jack-mumford/display-keyboard/main/main_screen.h

#pragma once

#include <string>

#include <esp_err.h>
#include <lvgl.h>

#include "event_ids.h"
#include "screen.h"

#define DISPLAY_MEMORY
#define DEBUG_STRING

constexpr lv_coord_t kAlbumArtworkWidth = 130;
constexpr lv_coord_t kAlbumArtworkHeight = 130;

class MainScreen : public Screen {
 public:
  explicit MainScreen(MainDisplay& display);
  ~MainScreen();

  esp_err_t Initialize();
  void SetWiFiStatus(WiFiStatus status);
  void UpdateTime();
#ifdef DEBUG_STRING
  void SetDebugString(const char* str);
#endif
  void SetAlbumArtwork(lv_img_dsc_t image);

 private:
  esp_err_t InitializeStatusBar();
  void UpdateWiFi();
  esp_err_t LoadWiFiImages();
  esp_err_t LoadGearImage();
  esp_err_t LoadSpotifyImage();
  esp_err_t CreateTimeLabel();
  esp_err_t CreateSongDataLabels();
  esp_err_t CreateAlbumArtwork();
  void UpdateRating();
  esp_err_t LoadRatingImages();

  lv_img_dsc_t album_cover_image_;
  lv_obj_t* lbl_test_ = nullptr;
  lv_obj_t* lbl_time_ = nullptr;
#ifdef DEBUG_STRING
  lv_obj_t* lbl_debug_msg_ = nullptr;
#endif
#ifdef DISPLAY_MEMORY
  lv_obj_t* lbl_memory_spiram_ = nullptr;
  lv_obj_t* lbl_memory_internal_ = nullptr;
#endif
  lv_obj_t* img_album_ = nullptr;
  lv_obj_t* img_wifi_online_ = nullptr;
  lv_obj_t* img_wifi_offline_ = nullptr;
  lv_obj_t* img_spotify_ = nullptr;
  lv_obj_t* img_gear_ = nullptr;
  lv_obj_t* img_thumbs_none_ = nullptr;
  lv_obj_t* img_thumbs_up_ = nullptr;
  std::string last_time_;
  WiFiStatus wifi_status_ = WiFiStatus::Offline;
};
