jack-mumford/display-keyboard/main/wifi.cc

#include "wifi.h"

#include <cstring>

#define LOG_LOCAL_LEVEL ESP_LOG_VERBOSE
#include <esp_log.h>
#include <esp_wifi.h>

#include "event_ids.h"

namespace {
constexpr char TAG[] = "WiFi";
constexpr size_t kMaxSSIDLen = 31;
constexpr size_t kMaxKeyLen = 63;
constexpr int kMaxNumConnectRetry = 10;

const char* wifi_event_name(wifi_event_t event) {
  switch (event) {
    case WIFI_EVENT_WIFI_READY:
      return "WIFI_EVENT_WIFI_READY";
    case WIFI_EVENT_SCAN_DONE:
      return "WIFI_EVENT_SCAN_DONE";
    case WIFI_EVENT_STA_START:
      return "WIFI_EVENT_STA_START";
    case WIFI_EVENT_STA_STOP:
      return "WIFI_EVENT_STA_STOP";
    case WIFI_EVENT_STA_CONNECTED:
      return "WIFI_EVENT_STA_CONNECTED";
    case WIFI_EVENT_STA_DISCONNECTED:
      return "WIFI_EVENT_STA_DISCONNECTED";
    case WIFI_EVENT_STA_AUTHMODE_CHANGE:
      return "WIFI_EVENT_STA_AUTHMODE_CHANGE";
    case WIFI_EVENT_STA_WPS_ER_SUCCESS:
      return "WIFI_EVENT_STA_WPS_ER_SUCCESS";
    case WIFI_EVENT_STA_WPS_ER_FAILED:
      return "WIFI_EVENT_STA_WPS_ER_FAILED";
    case WIFI_EVENT_STA_WPS_ER_TIMEOUT:
      return "WIFI_EVENT_STA_WPS_ER_TIMEOUT";
    case WIFI_EVENT_STA_WPS_ER_PIN:
      return "WIFI_EVENT_STA_WPS_ER_PIN";
    case WIFI_EVENT_STA_WPS_ER_PBC_OVERLAP:
      return "WIFI_EVENT_STA_WPS_ER_PBC_OVERLAP";
    case WIFI_EVENT_AP_START:
      return "WIFI_EVENT_AP_START";
    case WIFI_EVENT_AP_STOP:
      return "WIFI_EVENT_AP_STOP";
    case WIFI_EVENT_AP_STACONNECTED:
      return "WIFI_EVENT_AP_STACONNECTED";
    case WIFI_EVENT_AP_STADISCONNECTED:
      return "WIFI_EVENT_AP_STADISCONNECTED";
    case WIFI_EVENT_AP_PROBEREQRECVED:
      return "WIFI_EVENT_AP_PROBEREQRECVED";
    case WIFI_EVENT_FTM_REPORT:
      return "WIFI_EVENT_FTM_REPORT";
    case WIFI_EVENT_MAX:
      return "WIFI_EVENT_MAX";
    default:
      return "<unknown: wifi_event_t>";
  }
}

const char* ip_event_name(ip_event_t event) {
  switch (event) {
    case IP_EVENT_STA_GOT_IP:
      return "IP_EVENT_STA_GOT_IP";
    case IP_EVENT_STA_LOST_IP:
      return "IP_EVENT_STA_LOST_IP";
    case IP_EVENT_AP_STAIPASSIGNED:
      return "IP_EVENT_AP_STAIPASSIGNED";
    case IP_EVENT_GOT_IP6:
      return "IP_EVENT_GOT_IP6";
    case IP_EVENT_ETH_GOT_IP:
      return "IP_EVENT_ETH_GOT_IP";
    case IP_EVENT_PPP_GOT_IP:
      return "IP_EVENT_PPP_GOT_IP";
    case IP_EVENT_PPP_LOST_IP:
      return "IP_EVENT_PPP_LOST_IP";
    default:
      return "<unknown: ip_event_t>";
  }
}

void SafeStrCopy(char* dst, const char* src, size_t len) {
  std::strncpy(dst, src, len);
  dst[len - 1] = '\0';
}

esp_err_t GetHostname(esp_netif_t* netif, std::string* hostname) {
  const char* name(nullptr);
  const esp_err_t err = esp_netif_get_hostname(netif, &name);
  if (err != ESP_OK) {
    ESP_LOGD(TAG, "Can't get hostname: %s", esp_err_to_name(err));
    return err;
  }
  *hostname = name ? name : "";
  return ESP_OK;
}

esp_err_t GetIPAddress(esp_netif_t* netif, esp_ip4_addr_t* addr) {
  esp_netif_ip_info_t info;
  const esp_err_t err = esp_netif_get_ip_info(netif, &info);
  if (err != ESP_OK) {
    ESP_LOGD(TAG, "Can't get assigned IP address: %s", esp_err_to_name(err));
    return err;
  }
  *addr = info.ip;
  return ESP_OK;
}

}  // namespace

void WiFi::HandleWiFiEvent(wifi_event_t event_id, void* event_data) {
  ESP_LOGV(TAG, "Wi-Fi event: %s", wifi_event_name(event_id));
  switch (event_id) {
    case WIFI_EVENT_STA_START:
      ESP_LOGW(TAG, "Starting");
      esp_wifi_connect();
      break;
    case WIFI_EVENT_STA_DISCONNECTED:
      if (retry_num_ < kMaxNumConnectRetry) {
        esp_wifi_connect();
        retry_num_++;
      } else {
        ESP_LOGW(TAG, "Connection failed");
        xEventGroupSetBits(wifi_event_group_, EVENT_NETWORK_DISCONNECTED);
      }
      break;
    default:
      break;
  }
}

void WiFi::HandleIPEvent(ip_event_t event_id, void* event_data) {
  ESP_LOGV(TAG, "IP event: %s", ip_event_name(event_id));
  switch (event_id) {
    case IP_EVENT_STA_GOT_IP: {
      const ip_event_got_ip_t* event =
          static_cast<ip_event_got_ip_t*>(event_data);
      ESP_LOGI(TAG, "Got ip:" IPSTR, IP2STR(&event->ip_info.ip));
      std::string hostname = "?";
      ::GetHostname(event->esp_netif, &hostname);
      ESP_LOGI(TAG, "Hostname: \"%s\"", hostname.c_str());

      retry_num_ = 0;
      xEventGroupSetBits(wifi_event_group_, EVENT_NETWORK_GOT_IP);
    } break;
    default:
      break;
  }
}

// static
void WiFi::EventHandler(void* arg,
                        esp_event_base_t event_base,
                        int32_t event_id,
                        void* event_data) {
  if (event_base == WIFI_EVENT) {
    static_cast<WiFi*>(arg)->HandleWiFiEvent(
        static_cast<wifi_event_t>(event_id), event_data);
  } else if (event_base == IP_EVENT) {
    static_cast<WiFi*>(arg)->HandleIPEvent(static_cast<ip_event_t>(event_id),
                                           event_data);
  }
}

WiFi::WiFi(EventGroupHandle_t wifi_event_group)
    : wifi_event_group_(wifi_event_group),
      instance_any_id_(nullptr),
      instance_got_ip_(nullptr),
      retry_num_(0),
      netif_(nullptr) {}

WiFi::~WiFi() {
  if (instance_got_ip_) {
    ESP_ERROR_CHECK(esp_event_handler_instance_unregister(
        IP_EVENT, IP_EVENT_STA_GOT_IP, instance_got_ip_));
  }
  if (instance_any_id_) {
    ESP_ERROR_CHECK(esp_event_handler_instance_unregister(
        WIFI_EVENT, ESP_EVENT_ANY_ID, instance_any_id_));
  }
}

esp_err_t WiFi::Inititialize() {
  esp_err_t err = esp_netif_init();
  if (err != ESP_OK) {
    ESP_LOGE(TAG, "netif init failed: %s", esp_err_to_name(err));
    return err;
  }

  esp_netif_t* netif_ = esp_netif_create_default_wifi_sta();
  if (!netif_)
    return ESP_FAIL;

  const wifi_init_config_t cfg = WIFI_INIT_CONFIG_DEFAULT();
  err = esp_wifi_init(&cfg);
  if (err != ESP_OK) {
    ESP_LOGE(TAG, "esp_wifi_init failed: %s", esp_err_to_name(err));
    return err;
  }

  err = esp_event_handler_instance_register(
      WIFI_EVENT, ESP_EVENT_ANY_ID, &EventHandler, this, &instance_any_id_);
  if (err != ESP_OK) {
    ESP_LOGE(TAG, "esp_event_handler_instance_register failed: %s",
             esp_err_to_name(err));
    return err;
  }
  err = esp_event_handler_instance_register(
      IP_EVENT, IP_EVENT_STA_GOT_IP, &EventHandler, this, &instance_got_ip_);

  return err;
}

esp_err_t WiFi::InitiateConnection(const std::string& ssid,
                                   const std::string& key) {
  ESP_LOGI(TAG, "Attempting connection to WiFi network: \"%s\"", ssid.c_str());

  esp_wifi_stop();
  // TODO: Is clearing events necessary, or is this done automatically?
  constexpr EventBits_t kAllNetworkEvents =
      EVENT_NETWORK_GOT_IP | EVENT_NETWORK_DISCONNECTED;
  xEventGroupClearBits(wifi_event_group_, kAllNetworkEvents);

  retry_num_ = 0;

  if (ssid.length() > kMaxSSIDLen || key.length() > kMaxKeyLen)
    return ESP_ERR_INVALID_SIZE;

  esp_err_t err = esp_wifi_set_mode(WIFI_MODE_STA);
  if (err != ESP_OK) {
    ESP_LOGE(TAG, "Failure to set mode: %s", esp_err_to_name(err));
    return err;
  }

  wifi_config_t wifi_config = {
      .sta =
          {
              .ssid = {0},
              .password = {0},
              .scan_method = WIFI_FAST_SCAN,
              .bssid_set = false,
              .bssid = {0},
              .channel = 0,
              .listen_interval = 0,
              .sort_method = WIFI_CONNECT_AP_BY_SIGNAL,
              .threshold{
                  .rssi = 0,
                  .authmode = WIFI_AUTH_WPA2_PSK,
              },
              .pmf_cfg = {.capable = true, .required = false},
#if ESP_IDF_VERSION >= ESP_IDF_VERSION_VAL(4, 3, 0)
              .rm_enabled = false,
              .btm_enabled = false,
              .reserved = 0,
#endif
          },
  };
  SafeStrCopy(reinterpret_cast<char*>(wifi_config.sta.ssid), ssid.c_str(),
              sizeof(wifi_config.sta.ssid) - 1);
  SafeStrCopy(reinterpret_cast<char*>(wifi_config.sta.password), key.c_str(),
              sizeof(wifi_config.sta.password) - 1);

  err = esp_wifi_set_config(WIFI_IF_STA, &wifi_config);
  if (err != ESP_OK) {
    ESP_LOGE(TAG, "Failure to set config: %s", esp_err_to_name(err));
    return err;
  }

  err = esp_wifi_start();
  if (err != ESP_OK)
    ESP_LOGE(TAG, "Start failed: %s", esp_err_to_name(err));

  return err;
}

esp_err_t WiFi::GetHostname(std::string* hostname) const {
  return ::GetHostname(netif_, hostname);
}

esp_err_t WiFi::GetIPAddress(esp_ip4_addr_t* addr) const {
  return ::GetIPAddress(netif_, addr);
}
