jack-mumford/display-keyboard/main/keyboard.h

#pragma once

#include <array>

#include <esp_err.h>
#include <i2clib/master.h>
#include <i2clib/operation.h>

namespace kbd {
namespace adp5589 {
enum class RegNum : uint8_t;

namespace reg {
struct FIFO;
struct ID;
struct INT_STATUS;
struct PIN_CONFIG_A;
struct PIN_CONFIG_B;
struct PIN_CONFIG_C;
struct Status;
}  // namespace reg
}  // namespace adp5589
}  // namespace kbd

// Maximum number of HID_KEY_* key codes.
constexpr size_t kNumHIDKeyCodes = 0xff;

class Keyboard {
 public:
  explicit Keyboard(i2c::Master i2c_master);
  ~Keyboard();

  /**
   * Reset the keyboard IC to manufacturer default values.
   */
  esp_err_t Reset();

  /**
   * Initialize the keyboard.
   *
   * Call after reset to configure the keyboard IC.
   */
  esp_err_t Initialize();

  /**
   * Handle any keyboard events.
   *
   * Call this function, either polled or when interrupt pin indicates, to
   * handle any queued keyboard events.
   */
  esp_err_t HandleEvents();

 private:
  /**
   * Report all HID events to the USB host.
   */
  esp_err_t ReportHIDEvents();
  esp_err_t WriteByte(kbd::adp5589::RegNum reg, uint8_t value);
  esp_err_t ReadByte(kbd::adp5589::RegNum reg, uint8_t* value);
  esp_err_t Read(kbd::adp5589::reg::FIFO* reg);
  esp_err_t Read(kbd::adp5589::reg::ID* reg);
  esp_err_t Read(kbd::adp5589::reg::INT_STATUS* reg);
  esp_err_t Read(kbd::adp5589::reg::Status* reg);
  esp_err_t InitializeKeys(i2c::Operation& op);
  esp_err_t InitializeInterrupts(i2c::Operation& op);

  i2c::Master i2c_master_;

  /**
   * Array used to map TinyUSB's HID KEYCODE value to the button
   * pressed/depressed state.
   */
  std::array<bool, kNumHIDKeyCodes> key_states_;  // true if depressed.
  uint32_t event_number_ = 0;
};
