jack-mumford/display-keyboard/make.py

#!/usr/bin/env python3

import errno
import glob
import os
import platform
import serial.tools.list_ports
import subprocess
import sys
from pprint import pprint


class SdkConfigManager(object):
    @staticmethod
    def GetConsoleTarget(sdkconfig):
        if 'CONFIG_ESP_CONSOLE_UART' in sdkconfig and \
                sdkconfig['CONFIG_ESP_CONSOLE_UART'] == 'y':
            return 'UART'
        if 'CONFIG_ESP_CONSOLE_CDC' in sdkconfig and \
                sdkconfig['CONFIG_ESP_CONSOLE_CDC'] == 'y':
            return 'CDC'
        if 'CONFIG_ESP_CONSOLE_CUSTOM' in sdkconfig and \
                sdkconfig['CONFIG_ESP_CONSOLE_CUSTOM'] == 'y':
            return 'CUSTOM'
        return 'NONE'

    @staticmethod
    def Load():
        values = dict()
        try:
            with open('sdkconfig', 'r') as f:
                for line in f.readlines():
                    line = line.strip()
                    if len(line) < 1:
                        continue
                    if line[0] == '#':
                        continue
                    items = line.split('=')
                    if len(items) != 2:
                        print(line)
                    if items[0] in values:
                        print('Already have: ' + line)
                    values[items[0]] = items[1]
        except FileNotFoundError:
            pass
        return values


class PortManager(object):
    ignored = ('/dev/cu.Bluetooth-Incoming-Port')

    def __init__(self, sdkconfig):
        self.__sdkconfig = sdkconfig
        self.__console_target = SdkConfigManager.GetConsoleTarget(sdkconfig)

    @staticmethod
    def __GetSerialWildcard():
        return '/dev/cu.usbserial-*'

    @staticmethod
    def __GetModemWildcard():
        return '/dev/cu.usbmodem*'

    @staticmethod
    def __GetMatchingPorts(wildcard):
        ports = []
        for file in glob.glob(wildcard, recursive=False):
            if file in PortManager.ignored:
                continue
            ports.append(file)
        return ports

    @staticmethod
    def __GetDevicePorts():
        """Return any port with "USB Serial Device in the description.

        The ESP32 port is one of these.
        """
        ports = []
        for port in serial.tools.list_ports.comports():
            if (port.hwid and 'SER=0' in port.hwid):
                ports.append(port.device)
            # pprint(vars(port))
        return ports

    @staticmethod
    def __GetCOMPorts():
        """Return any port with "USB Serial Port" in the description.

        The serial debugger shows up as one of these.
        """
        ports = []
        for port in serial.tools.list_ports.comports():
            if (port.hwid and 'SER=0' not in port.hwid):
                ports.append(port.device)
            # pprint(vars(port))
        return ports

    @staticmethod
    def GetSerialPorts():
        if platform.system() == 'Windows':
            return PortManager.__GetCOMPorts()
        return PortManager.__GetMatchingPorts(
            PortManager.__GetSerialWildcard())

    @staticmethod
    def GetModemPorts():
        if platform.system() == 'Windows':
            return PortManager.__GetDevicePorts()
        return PortManager.__GetMatchingPorts(PortManager.__GetModemWildcard())

    @staticmethod
    def GetFlashPort():
        ports = PortManager.GetModemPorts()
        if ports:
            return ports[0]
        ports = PortManager.GetSerialPorts()
        return ports[0] if ports else None

    def GetMonitorPort(self):
        if self.__console_target == 'UART':
            ports = PortManager.GetSerialPorts()
        else:
            ports = PortManager.GetModemPorts()
        return ports[0] if ports else None

    def PrintPorts(self, fd=sys.stdout):
        print('Serial ports: %s' % PortManager.GetSerialPorts(), file=fd)
        print('Modem ports: %s' % PortManager.GetSerialPorts(), file=fd)
        print('Flash port: %s' % PortManager.GetFlashPort(), file=fd)
        print('Monitor port: %s' % self.GetMonitorPort(), file=fd)


def TargetNeedsMonitorPort(target):
    return target in ('monitor')


def TargetNeedsFlashPort(target):
    return target in ('flash', 'app-flash', 'flash-erase', 'manual-flash',
                      'flash-feathers2-stock-bootloader')


def MakeTargets(targets, port_manager):
    flash_port = PortManager.GetFlashPort()
    monitor_port = port_manager.GetMonitorPort()
    for target in targets:
        if TargetNeedsMonitorPort(target) and not monitor_port:
            print("Target \"%s\" needs a monitor port, but can't find one." %
                  target,
                  file=sys.stderr)
            port_manager.PrintPorts(sys.stderr)
            sys.exit(errno.ENODEV)
        if TargetNeedsFlashPort(target) and not flash_port:
            print("Target \"%s\" needs a flash port, but can't find one." %
                  target,
                  file=sys.stderr)
            port_manager.PrintPorts(sys.stderr)
            sys.exit(errno.ENODEV)
    if flash_port:
        os.environ["FLASH_PORT"] = flash_port
    if monitor_port:
        os.environ["MONITOR_PORT"] = monitor_port
    cmd = ['make', '--file=Makefile-build']
    cmd.extend(targets)
    subprocess.check_call(cmd)


if 'IDF_PATH' not in os.environ:
    print('ESP-IDF environment not sourced. Run:', file=sys.stderr)
    print(file=sys.stderr)
    print('. $HOME/esp/esp-idf/export.sh', file=sys.stderr)
    print(file=sys.stderr)
    sys.exit(1)

port_manager = PortManager(SdkConfigManager.Load())

targets = sys.argv[1:]
MakeTargets(targets, port_manager)
