jack-mumford/display-keyboard/main/event_ids.h

#pragma once

#include <freertos/include/freertos/FreeRTOS.h>

#include <freertos/include/freertos/event_groups.h>

constexpr EventBits_t EVENT_NETWORK_GOT_IP = BIT0;
constexpr EventBits_t EVENT_NETWORK_DISCONNECTED = BIT1;
constexpr EventBits_t EVENT_SPOTIFY_GOT_AUTHORIZATION_CODE = BIT2;
constexpr EventBits_t EVENT_SPOTIFY_ACCESS_TOKEN_GOOD = BIT3;
constexpr EventBits_t EVENT_SPOTIFY_ACCESS_TOKEN_FAILURE = BIT4;
constexpr EventBits_t EVENT_SPOTIFY_ACCESS_TOKEN_EXPIRE = BIT5;
constexpr EventBits_t EVENT_ALL = BIT0 | BIT1 | BIT2 | BIT3 | BIT4 | BIT5;

enum class WiFiStatus {
  Offline,
  Online,
};
