jack-mumford/display-keyboard/main/resource_fetcher.h

#pragma once

#include <cstdint>
#include <memory>
#include <queue>
#include <string>
#include <vector>

#include <freertos/include/freertos/FreeRTOS.h>
#include <freertos/include/freertos/event_groups.h>
#include <freertos/include/freertos/semphr.h>
#include <freertos/include/freertos/task.h>

#include <esp_err.h>
#include <esp_http_client/include/esp_http_client.h>
#include <lvgl.h>

/**
 * Clients using ResourceFetcher must implement this interface for
 * async fetch results.
 */
class ResourceFetchClient {
 public:
  /**
   * Called iff the successfully fetched resource is an image and was
   * successfully decompressed.
   */
  virtual void FetchImageResult(uint32_t request_id, lv_img_dsc_t image) = 0;

  /**
   * @brief Called when a resource request was completed successfully.
   *
   * @note check \p http_status_code for 200 before using \p resource_data.
   *
   * @warning Can be called on any thread/task.
   */
  virtual void FetchResult(uint32_t request_id,
                           int http_status_code,
                           std::vector<uint8_t> resource_data,
                           std::string mime_type) = 0;

  /**
   * @brief Called when an error occurred fetching a resource.
   *
   * @warning Can be called on any thread/task.
   */
  virtual void FetchError(uint32_t request_id, esp_err_t err) = 0;

 protected:
  ResourceFetchClient() = default;
  ~ResourceFetchClient() = default;
};

/**
 * @brief Download a single album cover image and then self delete.
 */
class ResourceFetcher {
 public:
  static ResourceFetcher* Start(ResourceFetchClient* fetch_client);

  /**
   * @brief Queue a resource to fetch.
   *
   * @note This is threadsafe.
   *
   * @param request_id
   * @param url
   */
  void QueueFetch(uint32_t request_id, std::string url);

 private:
  struct RequestData {
    RequestData(uint32_t request_id, std::string url)
        : request_id(request_id), url(std::move(url)) {}
    uint32_t request_id;
    std::string url;
  };
  static void IRAM_ATTR TaskFunc(void* arg);

  void IRAM_ATTR Run();
  void DecodeAndScaleJPEG(RequestData resource, std::vector<uint8_t> jpeg_data);
  void DownloadResource(RequestData resource);
  ResourceFetcher(ResourceFetchClient* fetch_client);
  ~ResourceFetcher() = default;

  esp_err_t Initialize();

  SemaphoreHandle_t mutex_;
  EventGroupHandle_t event_group_;    // Fetch events.
  std::queue<RequestData> requests_;  // Outstanding requests.
  ResourceFetchClient* fetch_client_;
  TaskHandle_t task_ = nullptr;
};
