jack-mumford/display-keyboard/main/https_client.h

#pragma once

#include <string>
#include <tuple>
#include <vector>

#include <esp_err.h>
#include <esp_http_client.h>

class HTTPSClient {
 public:
  using HeaderValue = std::pair<std::string, std::string>;

  HTTPSClient(std::string user_agent);
  ~HTTPSClient();

  esp_err_t DoGET(const std::string& url,
                  const std::vector<HeaderValue>& header_values,
                  std::string* response);

  esp_err_t DoPOST(const std::string& url,
                   const std::string& content,
                   const std::vector<HeaderValue>& header_values,
                   std::string* response);

  esp_err_t DoSSLCheck();

 private:
  static esp_err_t EventHandler(esp_http_client_event_t* evt);

  std::string CreateRequestString(
      const std::string& request_type,
      const std::string& host,
      const std::string& resource,
      const std::string& content,
      const std::vector<HeaderValue>& header_values) const;

  const std::string user_agent_;
  std::string last_request_data_;
};
