jack-mumford/display-keyboard/example_test.py

#!/usr/bin/env python

from __future__ import division
from __future__ import print_function
from __future__ import unicode_literals

import ttfw_idf


@ttfw_idf.idf_example_test(env_tag="Example_GENERIC", target=['esp32', 'esp32s2'], ci_target=['esp32'])
def test_examples_keyboard(env, extra_data):
    app_name = 'keyboard'
    dut = env.get_dut(app_name, "examples/get-started/keyboard")
    dut.start_app()
    res = dut.expect(ttfw_idf.MINIMUM_FREE_HEAP_SIZE_RE)
    if not res:
        raise ValueError('Maximum heap size info not found')
    ttfw_idf.print_heap_size(app_name, dut.app.config_name, dut.TARGET, res[0])


if __name__ == '__main__':
    test_examples_keyboard()
